altita-tech/ERB4U/Images/erb4u-8-side-head-3d-altium-cn.png

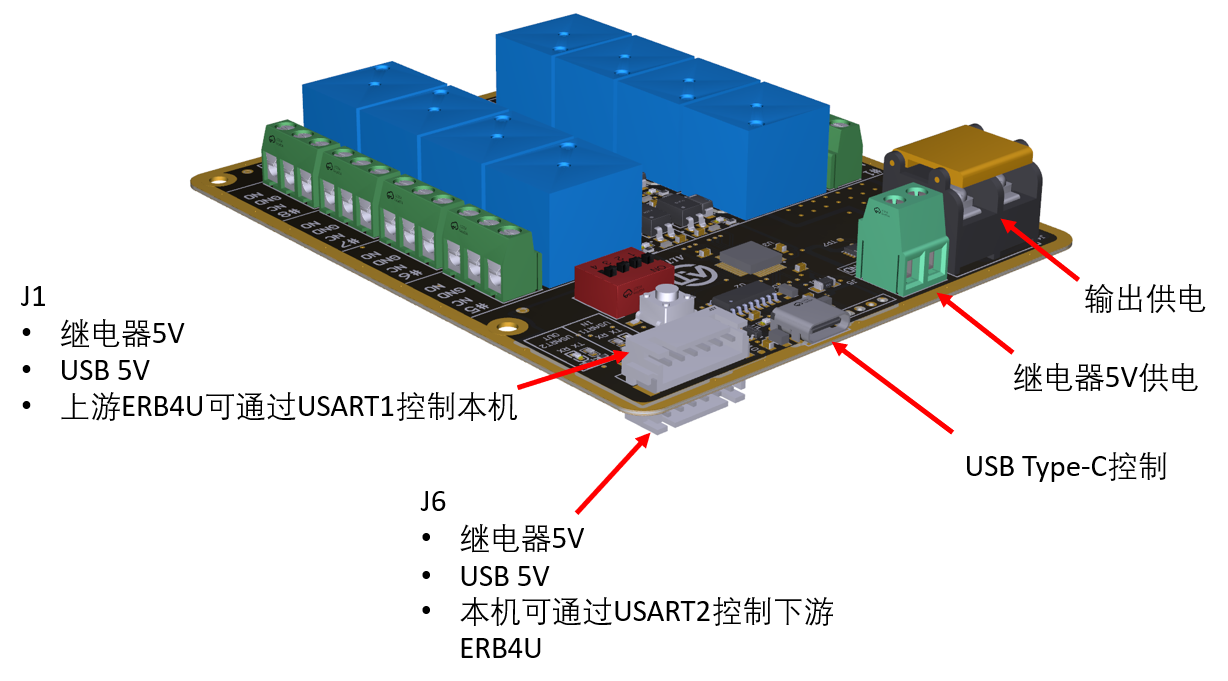
Images/erb4u-8-side-head-3d-altium-cn.png
