altita-tech/ERB4U/Images/erb4u-8-side-head-3d-altium.png

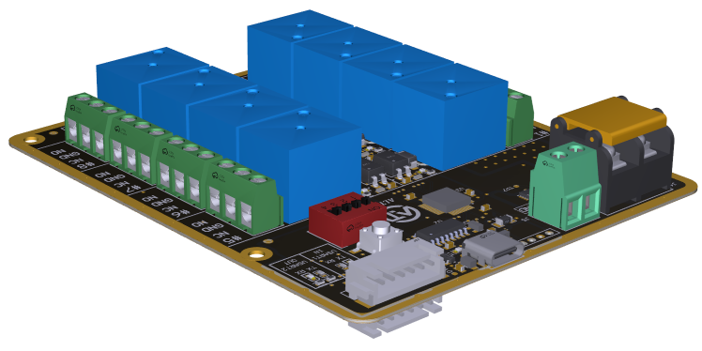
Images/erb4u-8-side-head-3d-altium.png
